RADARC/Scout-Radio/Kicad/Scout_radio/3D_Models/3214G.stp

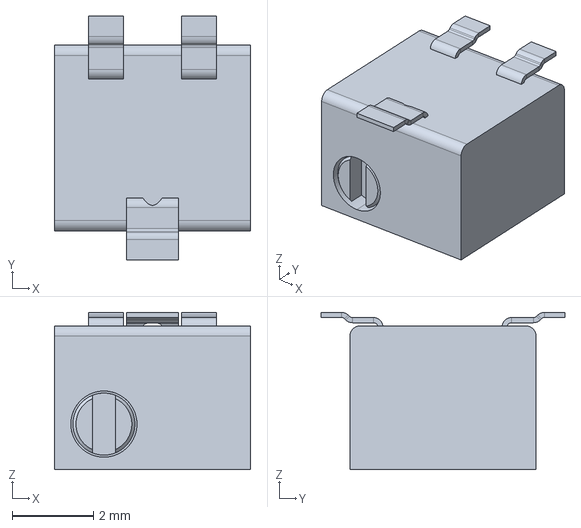
[picture p30: CAD file, 2024-11-30]
Kicad/Scout_radio/3D_Models/3214G.stp
4.83 x 5.99 x 3.86 mm
