RADARC/Scout-Radio/Kicad/Scout_radio/3D_Models/EVQ-WKA001--3DModel-STEP-56544.STEP

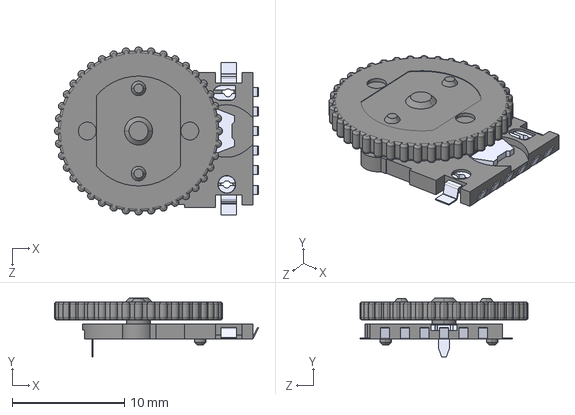
[picture p31: CAD file, 2024-11-30]
Kicad/Scout_radio/3D_Models/EVQ-WKA001--3DModel-STEP-56544.STEP
18.2 x 5.25 x 15.0 mm
