RADARC/Scout-Radio/Kicad/Scout_radio/3D_Models/18650 Battery Holder v5.step

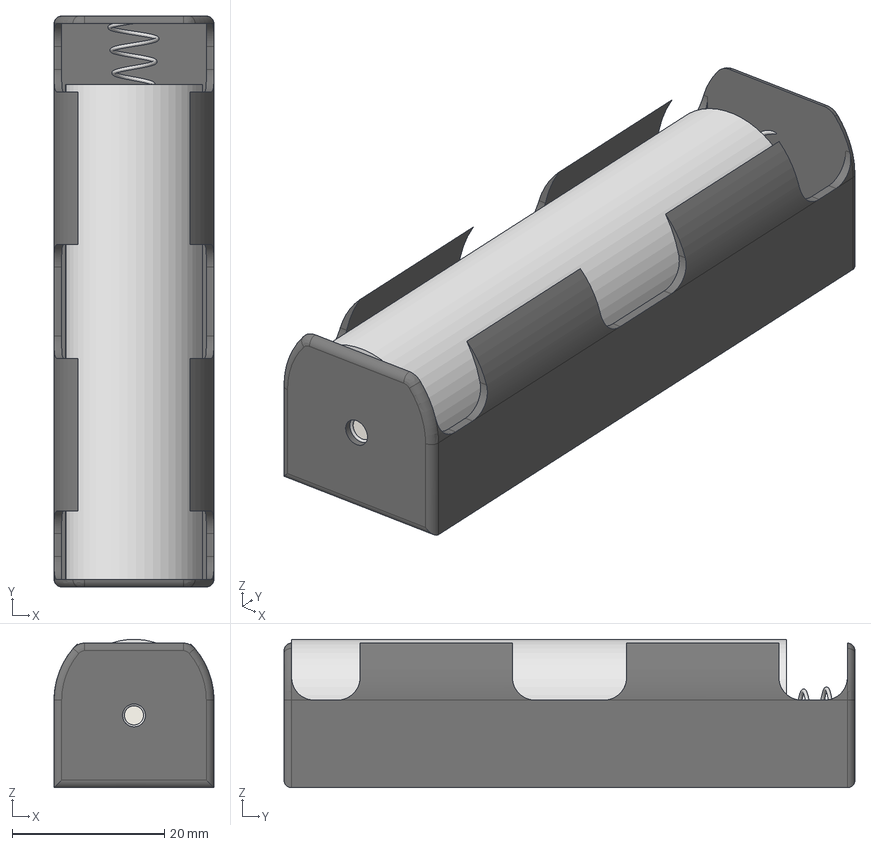
[picture p32: CAD file, 2024-11-30]
Kicad/Scout_radio/3D_Models/18650 Battery Holder v5.step
21.0 x 75.0 x 19.5 mm
