RADARC/Scout-Radio/software/Morse/MorseFlash.py

# SPDX-FileCopyrightText: 2017 Collin Cunningham for Adafruit Industries
#
# SPDX-License-Identifier: MIT

# Circuit Playground Express CircuitPython Morse Code Flasher
# This is meant to work with the Circuit Playground Express board:
#   https://www.adafruit.com/product/3333
# Needs the NeoPixel module installed:
#   https://github.com/adafruit/Adafruit_CircuitPython_NeoPixel
# Author: Collin Cunningham
# License: MIT License (https://opensource.org/licenses/MIT)

import time
from digitalio import DigitalInOut, Direction
import board
import pwmio

torch = DigitalInOut(board.GP16)
torch.direction = Direction.OUTPUT

tone = pwmio.PWMOut(board.GP20, duty_cycle=0, frequency=440, variable_frequency=False)

# Configuration:
# Message to display (capital letters and numbers only)
message = 'RADARC'
dot_length = 0.15  # Duration of one Morse dot
dash_length = (dot_length * 3.0)  # Duration of one Morse dash
symbol_gap = dot_length  # Duration of gap between dot or dash
character_gap = (dot_length * 3.0)  # Duration of gap between characters

morse = [
    ('A', '.-'),
    ('B', '-...'),
    ('C', '-.-.'),
    ('D', '-..'),
    ('E', '.'),
    ('F', '..-.'),
    ('G', '--.'),
    ('H', '....'),
    ('I', '..'),
    ('J', '.---'),
    ('K', '-.-'),
    ('L', '.-..'),
    ('M', '--'),
    ('N', '-.'),
    ('O', '---'),
    ('P', '.--.'),
    ('Q', '--.-'),
    ('R', '.-.'),
    ('S', '...'),
    ('T', '-'),
    ('U', '..-'),
    ('V', '...-'),
    ('W', '.--'),
    ('X', '-..-'),
    ('Y', '-.--'),
    ('Z', '--..'),
    ('0', '-----'),
    ('1', '.----'),
    ('2', '..---'),
    ('3', '...--'),
    ('4', '....-'),
    ('5', '.....'),
    ('6', '-....'),
    ('7', '--...'),
    ('8', '---..'),
    ('9', '----.'),
]


# Define a class that represents the morse flasher.


class MorseFlasher:
   

    def light(self, on=False):
        if on:
            torch.value = True
            tone.duty_cycle = 65535 // 2  # On 50%
            
        else:
            torch.value = False
            tone.duty_cycle = 0

    def showDot(self):
        self.light(True)
        time.sleep(dot_length)
        self.light(False)
        time.sleep(symbol_gap)

    def showDash(self):
        self.light(True)
        time.sleep(dash_length)
        self.light(False)
        time.sleep(symbol_gap)

    def encode(self, string):
        output = ""
        # iterate through string's characters
        for c in string:
            # find morse code for a character
            for x in morse:
                if x[0] == c:
                    # add code to output
                    output += x[1]
            # add a space in between characters
            output += " "
        # save complete morse code output to display
        self.display(output)

    def display(self, code=".-.-.- "):
        # iterate through morse code symbols
        for c in code:
            # show a dot
            if c == ".":
                self.showDot()
            # show a dash
            elif c == "-":
                self.showDash()
            # show a gap
            elif c == " ":
                time.sleep(character_gap)




# Create a morse flasher object.
flasher = MorseFlasher()

# Main loop will run forever
while True:
    flasher.encode(message)
