RADARC/Scout-Radio/software/LSM303/lsm303_accel_simpletest.py

# SPDX-FileCopyrightText: 2021 ladyada for Adafruit Industries
# SPDX-License-Identifier: MIT

""" Display accelerometer data once per second """

import time
import board
import busio

import adafruit_lsm303_accel

i2c = busio.I2C(board.GP5, board.GP4)


sensor = adafruit_lsm303_accel.LSM303_Accel(i2c)

while True:
    acc_x, acc_y, acc_z = sensor.acceleration

    print(
        "Acceleration (m/s^2): ({0:10.3f}, {1:10.3f}, {2:10.3f})".format(
            acc_x, acc_y, acc_z
        )
    )
    print("")
    time.sleep(1.0)
